Corteil/rp2350-hdmi-hexpansion/firmware/pio-testcard/src/fs_image.h

// GENERATED FILE -- do not hand-edit.
// Produced by tools/build_fs_image.py from badge_app/app.py. Re-run that
// script (pip install littlefs-python; MPY_CROSS pointing at a matching
// mpy-cross build -- see the script's header comment) after changing
// app.py, then rebuild this firmware.

#ifndef FS_IMAGE_H
#define FS_IMAGE_H

#include <stdint.h>

#define FS_IMAGE_BLOCK_SIZE  512
#define FS_IMAGE_BLOCK_COUNT 15
#define FS_IMAGE_SIZE 7680

static const uint8_t fs_image[FS_IMAGE_SIZE] = {
    0x02, 0x00, 0x00, 0x00, 0xf0, 0x0f, 0xff, 0xf7, 0x6c, 0x69, 0x74, 0x74, 0x6c, 0x65, 0x66, 0x73,
    0x2f, 0xe0, 0x00, 0x10, 0x01, 0x00, 0x02, 0x00, 0x00, 0x02, 0x00, 0x00, 0x0f, 0x00, 0x00, 0x00,
    0xff, 0x00, 0x00, 0x00, 0xff, 0xff, 0xff, 0x7f, 0xfe, 0x03, 0x00, 0x00, 0x20, 0x00, 0x04, 0x1f,
    0x61, 0x70, 0x70, 0x2e, 0x6d, 0x70, 0x79, 0x20, 0x00, 0x00, 0x07, 0x70, 0x1f, 0xf9, 0xc1, 0xe1,
    0x27, 0x49, 0x0b, 0xff, 0xff, 0xff, 0xff, 0xff, 0xff, 0xff, 0xff, 0xff, 0xff, 0xff, 0xff, 0xff,
    0xff, 0xff, 0xff, 0xff, 0xff, 0xff, 0xff, 0xff, 0xff, 0xff, 0xff, 0xff, 0xff, 0xff, 0xff, 0xff,
    0xff, 0xff, 0xff, 0xff, 0xff, 0xff, 0xff, 0xff, 0xff, 0xff, 0xff, 0xff, 0xff, 0xff, 0xff, 0xff,
    0xff, 0xff, 0xff, 0xff, 0xff, 0xff, 0xff, 0xff, 0xff, 0xff, 0xff, 0xff, 0xff, 0xff, 0xff, 0xff,
    0xff, 0xff, 0xff, 0xff, 0xff, 0xff, 0xff, 0xff, 0xff, 0xff, 0xff, 0xff, 0xff, 0xff, 0xff, 0xff,
    0xff, 0xff, 0xff, 0xff, 0xff, 0xff, 0xff, 0xff, 0xff, 0xff, 0xff, 0xff, 0xff, 0xff, 0xff, 0xff,
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
    0xff, 0xff, 0xff, 0xff, 0xff, 0xff, 0xff, 0xff, 0xff, 0xff, 0xff, 0xff, 0xff, 0xff, 0xff, 0xff,
    0xff, 0xff, 0xff, 0xff, 0xff, 0xff, 0xff, 0xff, 0xff, 0xff, 0xff, 0xff, 0xff, 0xff, 0xff, 0xff,
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
};

#endif
